mot-prog/avr-programmer/firmware/VirtualSerial/VirtualSerial.c

#include <avr/io.h>
#include <util/delay.h>
#include "VirtualSerial.h"

#define b7 0b10000000
#define b6 0b01000000

USB_ClassInfo_CDC_Device_t VirtualSerial_CDC_Interface =
	{
		.Config =
			{
				.ControlInterfaceNumber = INTERFACE_ID_CDC_CCI,
				.DataINEndpoint =
					{
						.Address = CDC_TX_EPADDR,
						.Size = CDC_TXRX_EPSIZE,
						.Banks = 1,
					},
				.DataOUTEndpoint =
					{
						.Address = CDC_RX_EPADDR,
						.Size = CDC_TXRX_EPSIZE,
						.Banks = 1,
					},
				.NotificationEndpoint =
					{
						.Address = CDC_NOTIFICATION_EPADDR,
						.Size = CDC_NOTIFICATION_EPSIZE,
						.Banks = 1,
					},
			},
};

/** Standard file stream for the CDC interface when set up, so that the virtual CDC COM port can be
 *  used like any regular character stream in the C APIs.
 */
static FILE USBSerialStream;

/** Main program entry point. This routine contains the overall program flow, including initial
 *  setup of all components and the main program loop.
 */
int main(void)
{
	SetupHardware();

	/* Create a regular character stream for the interface so that it can be used with the stdio.h functions */
	CDC_Device_CreateStream(&VirtualSerial_CDC_Interface, &USBSerialStream);

	LEDs_SetAllLEDs(LEDMASK_USB_NOTREADY);
	GlobalInterruptEnable();

	for (;;)
	{
		CheckButtons();

		/* Must throw away unused bytes from the host, or it will lock up while waiting for the device */
		CDC_Device_ReceiveByte(&VirtualSerial_CDC_Interface);

		CDC_Device_USBTask(&VirtualSerial_CDC_Interface);
		USB_USBTask();
	}
}

/** Configures the board hardware and chip peripherals for the demo's functionality. */
void SetupHardware(void)
{
#if (ARCH == ARCH_AVR8)
	/* Disable watchdog if enabled by bootloader/fuses */
	MCUSR &= ~(1 << WDRF);
	wdt_disable();

	/* Disable clock division */
	clock_prescale_set(clock_div_1);
#elif (ARCH == ARCH_XMEGA)
	/* Start the PLL to multiply the 2MHz RC oscillator to 32MHz and switch the CPU core to run from it */
	XMEGACLK_StartPLL(CLOCK_SRC_INT_RC2MHZ, 2000000, F_CPU);
	XMEGACLK_SetCPUClockSource(CLOCK_SRC_PLL);

	/* Start the 32MHz internal RC oscillator and start the DFLL to increase it to 48MHz using the USB SOF as a reference */
	XMEGACLK_StartInternalOscillator(CLOCK_SRC_INT_RC32MHZ);
	XMEGACLK_StartDFLL(CLOCK_SRC_INT_RC32MHZ, DFLL_REF_INT_USBSOF, F_USB);

	PMIC.CTRL = PMIC_LOLVLEN_bm | PMIC_MEDLVLEN_bm | PMIC_HILVLEN_bm;
#endif

	// /* Hardware Initialization */
	// Joystick_Init();
	// LEDs_Init();
	DDRC &= 0x00;
	PORTC |= (b6 | b7);
	USB_Init();
}

int Button_Status(int boutton)
{
	return (PINC & boutton) == 0;
}

void CheckButtons(void)
{
	char *ReportString = NULL;
	static bool ActionSent = false;

	if (Button_Status(b6) && Button_Status(b7))
	{
		ReportString = "\033[1;32mboth pressed\033[0m\r\n";
		_delay_ms(250);
		ActionSent = false;
	}
	else if (Button_Status(b6))
	{
		ReportString = "\033[1;31mb6 pressed\033[0m\r\n";
		_delay_ms(250);
		ActionSent = false;
	}
	else if (Button_Status(b7))
	{
		ReportString = "\033[1;33mb7 pressed\033[0m\r\n";
		_delay_ms(250);
		ActionSent = false;
	}

	if ((ReportString != NULL) && (ActionSent == false))
	{
		ActionSent = true;

		/* Write the string to the virtual COM port via the created character stream */
		fputs(ReportString, &USBSerialStream);

		/* Alternatively, without the stream: */
		// CDC_Device_SendString(&VirtualSerial_CDC_Interface, ReportString);
	}
}

/** Event handler for the library USB Connection event. */
void EVENT_USB_Device_Connect(void)
{
	LEDs_SetAllLEDs(LEDMASK_USB_ENUMERATING);
}

/** Event handler for the library USB Disconnection event. */
void EVENT_USB_Device_Disconnect(void)
{
	LEDs_SetAllLEDs(LEDMASK_USB_NOTREADY);
}

/** Event handler for the library USB Configuration Changed event. */
void EVENT_USB_Device_ConfigurationChanged(void)
{
	bool ConfigSuccess = true;

	ConfigSuccess &= CDC_Device_ConfigureEndpoints(&VirtualSerial_CDC_Interface);

	LEDs_SetAllLEDs(ConfigSuccess ? LEDMASK_USB_READY : LEDMASK_USB_ERROR);
}

/** Event handler for the library USB Control Request reception event. */
void EVENT_USB_Device_ControlRequest(void)
{
	CDC_Device_ProcessControlRequest(&VirtualSerial_CDC_Interface);
}

/** CDC class driver callback function the processing of changes to the virtual
 *  control lines sent from the host..
 *
 *  \param[in] CDCInterfaceInfo  Pointer to the CDC class interface configuration structure being referenced
 */
void EVENT_CDC_Device_ControLineStateChanged(USB_ClassInfo_CDC_Device_t *const CDCInterfaceInfo)
{
	/* You can get changes to the virtual CDC lines in this callback; a common
	   use-case is to use the Data Terminal Ready (DTR) flag to enable and
	   disable CDC communications in your application when set to avoid the
	   application blocking while waiting for a host to become ready and read
	   in the pending data from the USB endpoints.
	*/
	bool HostReady = (CDCInterfaceInfo->State.ControlLineStates.HostToDevice & CDC_CONTROL_LINE_OUT_DTR) != 0;

	(void)HostReady;
}
